hans61/Galaksija/Keyboard/eagle/rev2/Galaksija keyboard matrix.brd.png

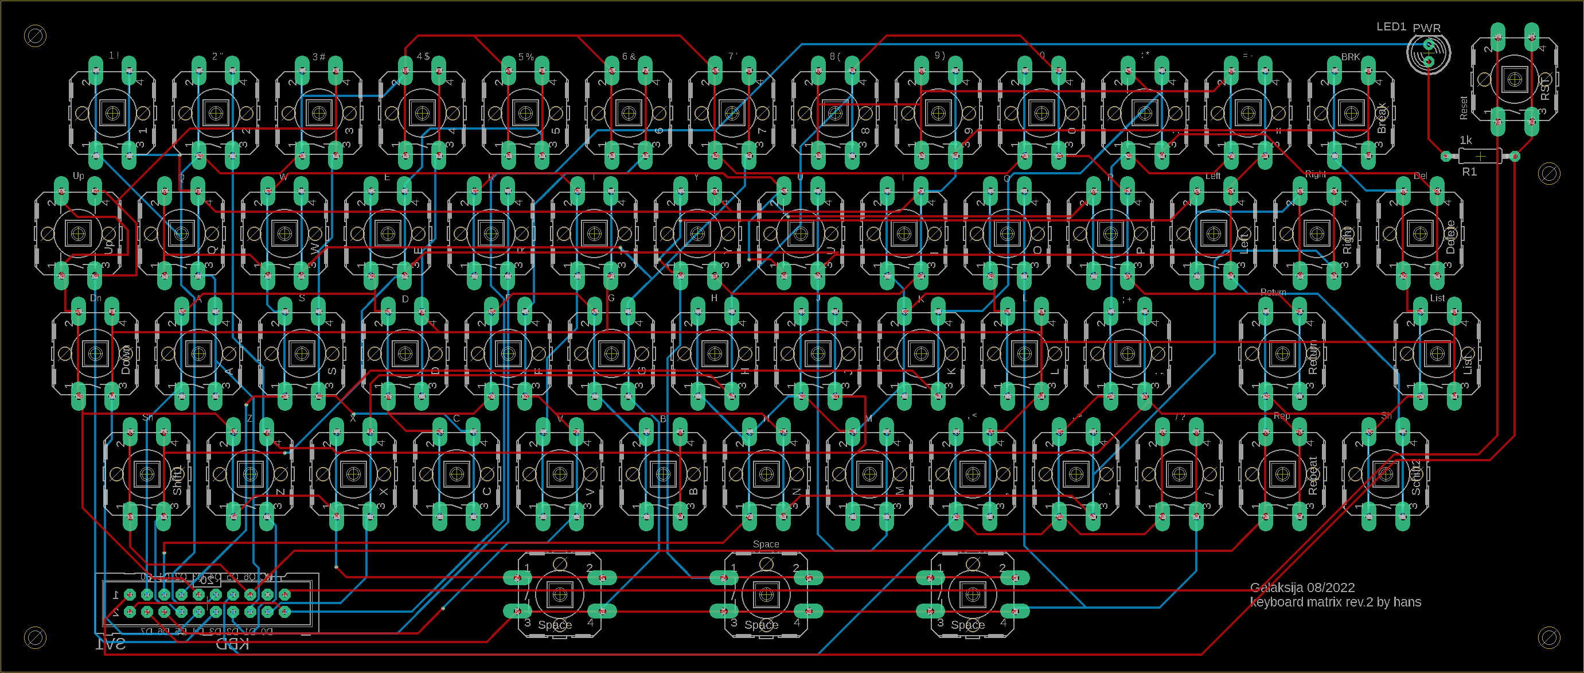
Keyboard/eagle/rev2/Galaksija keyboard matrix.brd.png
