hans61/Galaksija/Keyboard/eagle/rev2/Galaksija keyboard matrix.sch.png

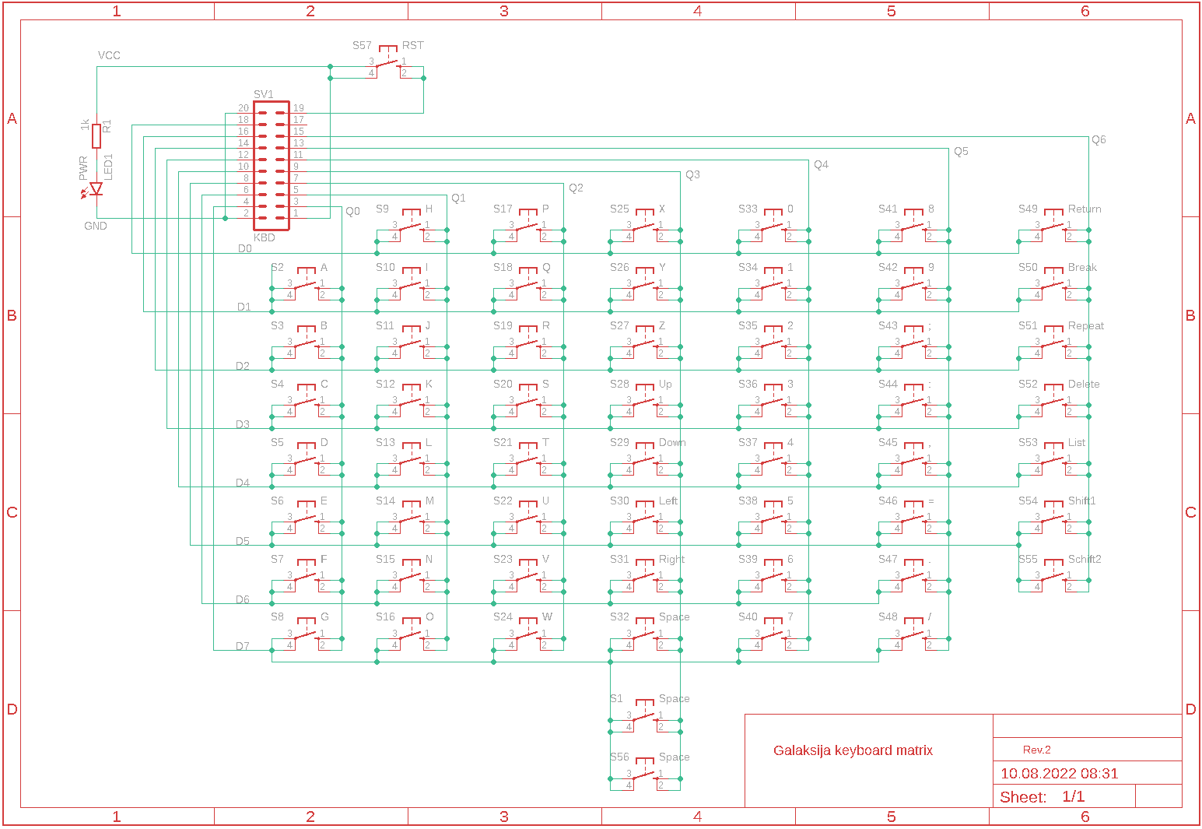
Keyboard/eagle/rev2/Galaksija keyboard matrix.sch.png
