hans61/Galaksija/Keyboard/Galaksija keyboard adapter.brd.png

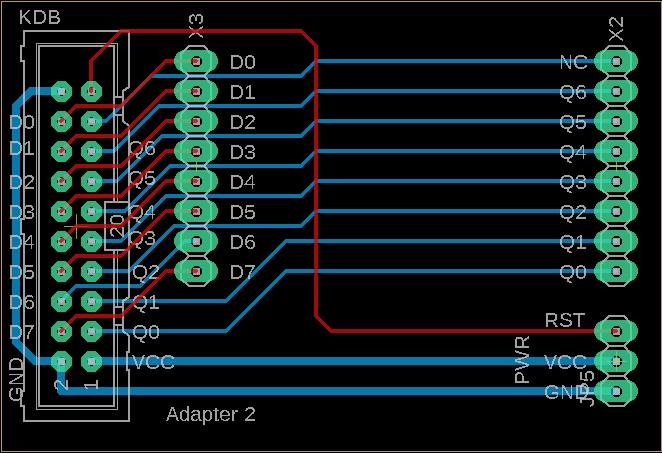
Keyboard/Galaksija keyboard adapter.brd.png
