hans61/Galaksija/Keyboard/Galaksija keyboard adapter.sch.png

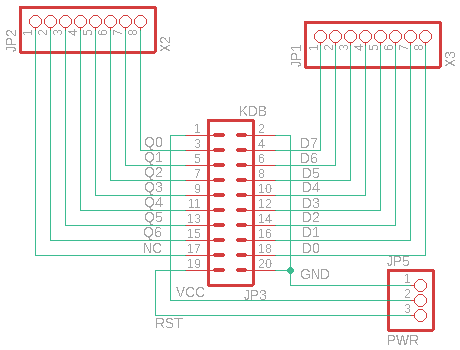
Keyboard/Galaksija keyboard adapter.sch.png
