hans61/Galaksija/Keyboard/Galaksija keyboard cover-m.png

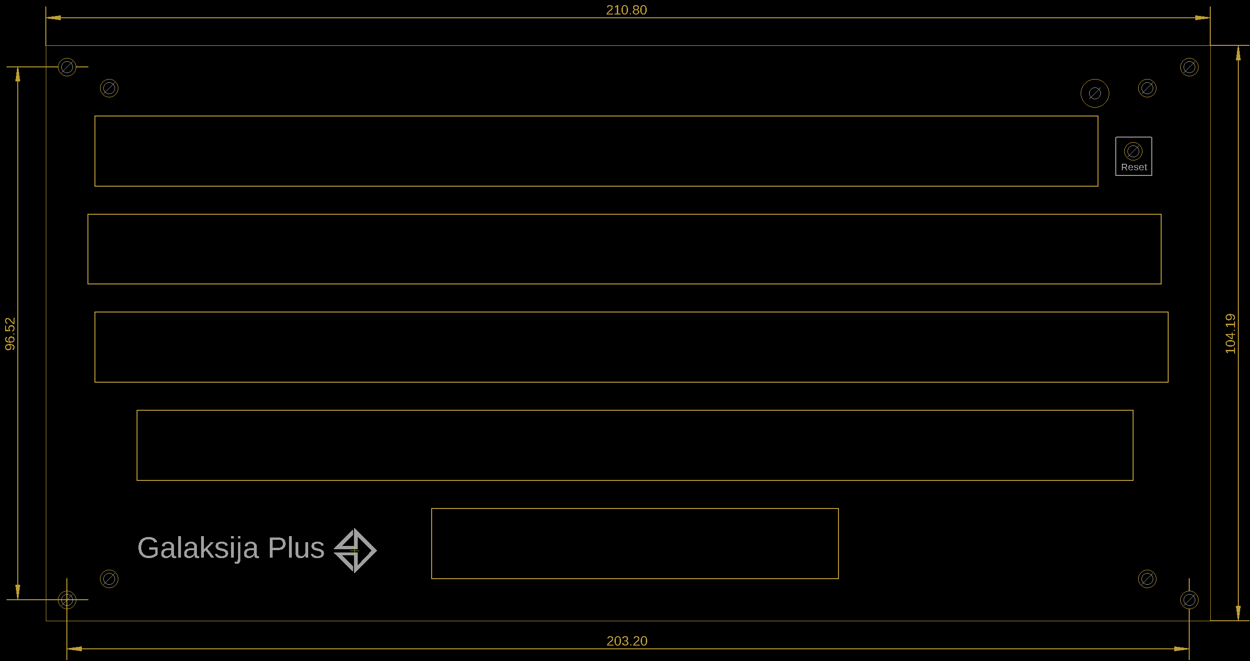
Keyboard/Galaksija keyboard cover-m.png
