hans61/Galaksija/Keyboard/Galaksija keyboard cover.png

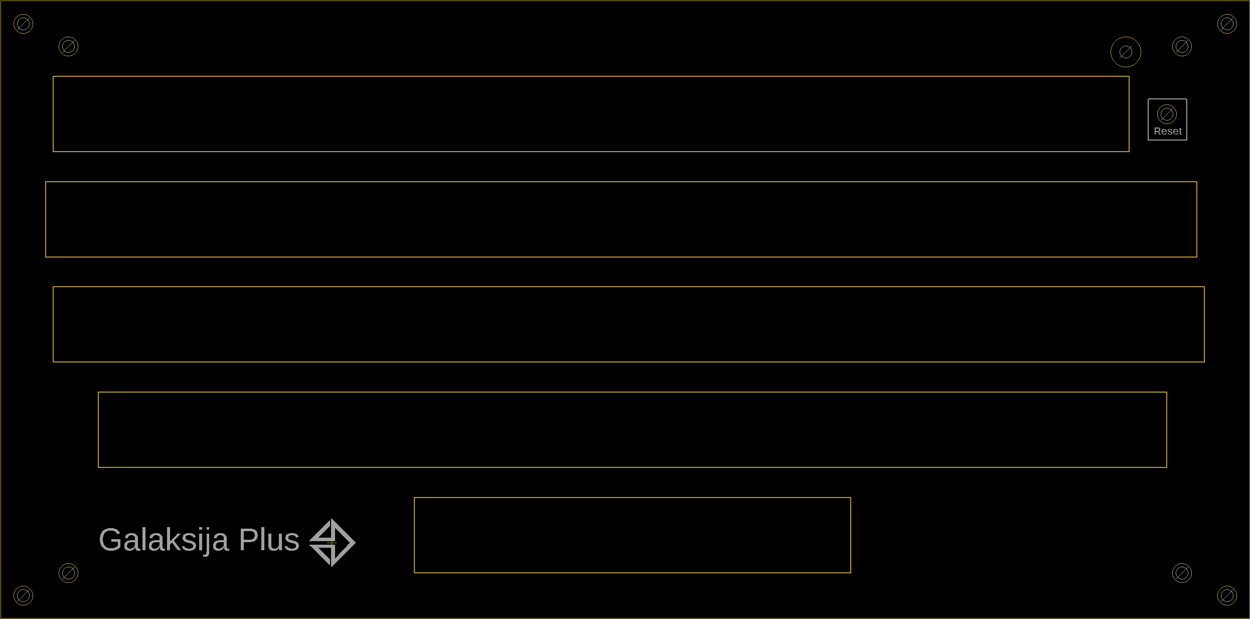
Keyboard/Galaksija keyboard cover.png
