hans61/Galaksija/Keyboard/Galaksija keyboard matrix top-m.png

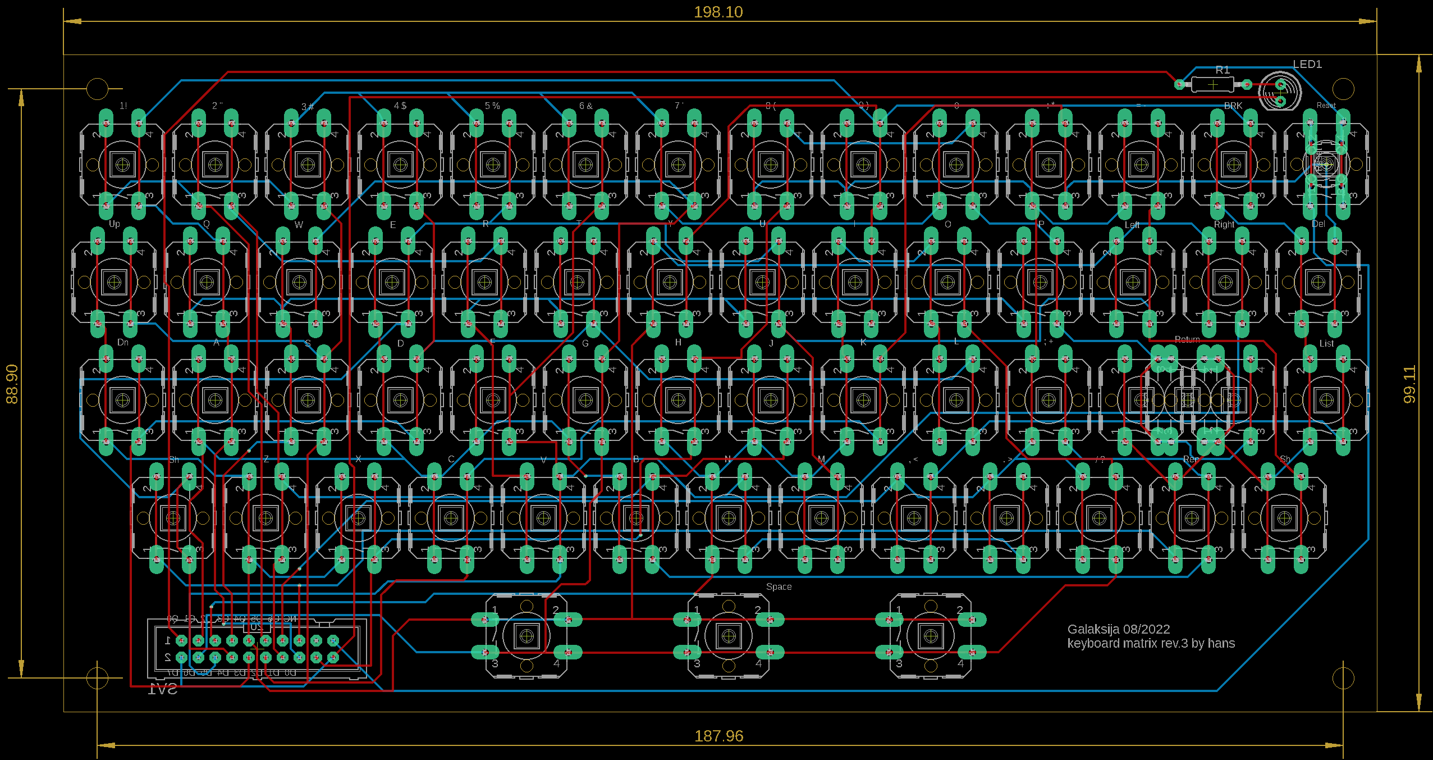
Keyboard/Galaksija keyboard matrix top-m.png
